Cosmin-DB/SAcre/documentation/pcb_preparacion/antes.png

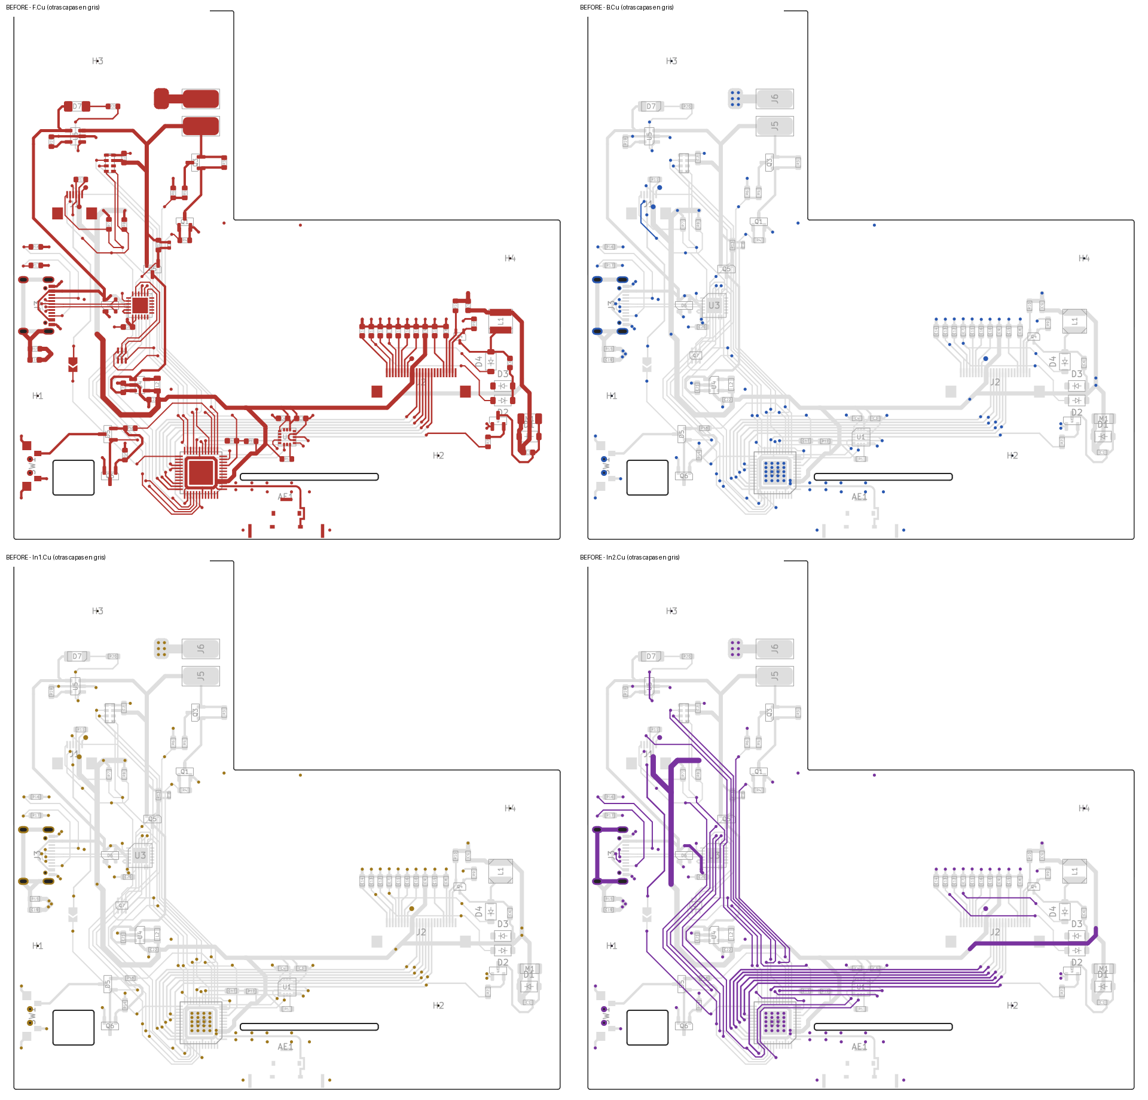
documentation/pcb_preparacion/antes.png
